totoche974/TLC-Mach3/src/manivelle.cpp

#include <Arduino.h>
#include <BleKeyboard.h>
#include <AiEsp32RotaryEncoder.h>

#include "manivelle.h"
#include "boutonMach3.h"
#include "screen.h"
#include "sleep.h"
#include "axe.h"

extern BleKeyboard keyboard;

#define ROTARY_ENCODER_STEPS 4

// extern BleKeyboard keyboard;

// instead of changing here, rather change numbers above
AiEsp32RotaryEncoder rotaryEncoder = AiEsp32RotaryEncoder(ROTARY_ENCODER_A_PIN, ROTARY_ENCODER_B_PIN,
                                                          ROTARY_ENCODER_BUTTON_PIN, ROTARY_ENCODER_VCC_PIN,
                                                          ROTARY_ENCODER_STEPS);

void initManivelle()
{
  // we must initialize rotary encoder
  rotaryEncoder.begin();

  rotaryEncoder.setup(
      []
      {
        rotaryEncoder.readEncoder_ISR();
      },
      [] {});

  rotaryEncoder.setAcceleration(250);
}

int previousEncoderPosition = 0;

const int KEY_2 = KEY_DOWN_ARROW;  // 40;
const int KEY_4 = KEY_LEFT_ARROW;  // 37; // KEY_LEFT_ARROW; //100; // 52; // X- : 100
const int KEY_6 = KEY_RIGHT_ARROW; // 39; // KEY_RIGHT_ARROW; // 102; // 54; // X+ : 102
const int KEY_8 = KEY_UP_ARROW;    // 38;

Axe currentAxe = Axe_x;
Axe previousAxe = Axe_x;
uint8_t selectedAxePositiveKey;
uint8_t selectedAxeNegativeKey;

void printAxe(Axe axeValue)
{
  switch (axeValue)
  {
  case Axe_x:
    printf("Axe X\n");
    screenSendMessage("   Axe X ");
    break;
  case Axe_y:
    printf("Axe Y\n");
    screenSendMessage("   Axe Y ");
    break;
  case Axe_z:
    printf("Axe Z\n");
    screenSendMessage("   Axe Z ");
    break;
  case Axe_a:
    printf("Axe A\n");
    screenSendMessage("   Axe A ");
    break;
  }
}

void selectAxe()
{
  currentAxe = getCurrentAxe();

  if (previousAxe != currentAxe)
  {
    switch (currentAxe)
    {
    case Axe_x:
    {
      selectedAxePositiveKey = KEY_4; // ACSII 4 : 52
      selectedAxeNegativeKey = KEY_6; // ACSII 6 : 54
      // Serial.print("currentAxe__X = ");
      // Serial.println(currentAxe);
      refreshSleepOriginTimestamp();
      break;
    }
    case Axe_y:
    {
      selectedAxePositiveKey = KEY_8; // ACSII 8 : 56
      selectedAxeNegativeKey = KEY_2; // ACSII 2 : 50
      // Serial.print("currentAxe__Y = ");
      // Serial.println(currentAxe);
      refreshSleepOriginTimestamp();
      break;
    }
    case Axe_z:
    {
      selectedAxePositiveKey = KEY_PAGE_UP;
      selectedAxeNegativeKey = KEY_PAGE_DOWN;
      // Serial.print("currentAxe__Z = ");
      // Serial.println(currentAxe);
      refreshSleepOriginTimestamp();
      break;
    }
    case Axe_a:
    {
      selectedAxePositiveKey = KEY_HOME;
      selectedAxeNegativeKey = KEY_END;
      // Serial.print("currentAxe__A = ");
      // Serial.println(currentAxe);
      refreshSleepOriginTimestamp();
      break;
    }
    }

    printAxe(currentAxe);
  }

  previousAxe = currentAxe;
}

void manivelle()
{
  // Serial.print("PIN_SECU_BT = "); Serial.println(digitalRead(PIN_SECU_BT));
  selectAxe();

  int currentEncoderPosition = -rotaryEncoder.readEncoder();
  int deltaEncoder = currentEncoderPosition - previousEncoderPosition;
  if ((digitalRead(PIN_SECU_BT) == LOW))
  { /* Touche Ctrl à droite ou à gauche*/
    refreshSleepOriginTimestamp();
    // Serial.print("PIN_SECU_BT = "); Serial.println(digitalRead(PIN_SECU_BT));
    if (deltaEncoder != 0)
    {
      printAxe(getCurrentAxe());
      printf("deltaEncoder: %d\n", deltaEncoder);
    }
    if (deltaEncoder > 0)
    {

      printf("CodRotIncrement > 0\n");
      // keyboard.press(KEY_LEFT_CTRL);
      printf("commande %d\n\n", selectedAxePositiveKey);
      keyboard.press(selectedAxePositiveKey);
      delay(50);
      keyboard.releaseAll();
    }
    else if (deltaEncoder < 0)
    {

      printf("CodRotIncrement < 0\n");
      // keyboard.press(KEY_LEFT_CTRL);
      printf("commande %d\n\n", selectedAxeNegativeKey);
      keyboard.press(selectedAxeNegativeKey);
      delay(50);
      keyboard.releaseAll();
    }
  }
  previousEncoderPosition = currentEncoderPosition;
}
