totoche974/TLC-Mach3/example_basic/fuel_jauge_lipo/fuel_jauge.cpp

//https://how2electronics.com/interfacing-max17043-lipo-fuel-gauge-ic-with-arduino/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

#include <SPI.h>
#include <Wire.h>
#include <LiFuelGauge.h>        //https://github.com/nlamprian/LiFuelGauge
#include <Adafruit_GFX.h>
#include <Adafruit_SSD1306.h>
 
#define SCREEN_WIDTH 128    // OLED display width, in pixels
#define SCREEN_HEIGHT 64    // OLED display height, in pixels
#define OLED_RESET     4    // Reset pin # (or -1 if sharing Arduino reset pin)
#define SCREEN_ADDRESS 0x3C // 0x3D for 128x64, 0x3C for 128x32
Adafruit_SSD1306 display(SCREEN_WIDTH, SCREEN_HEIGHT, &Wire, OLED_RESET);
 
 
void lowPower();
 
LiFuelGauge gauge(MAX17043, 0, lowPower);
 
volatile boolean alert = false;
 
 
void setup()
{
  Serial.begin(9600); // Initializes serial port
  if (!display.begin(SSD1306_SWITCHCAPVCC, SCREEN_ADDRESS))
  {
    Serial.println(F("SSD1306 allocation failed"));
    for (;;); // Don't proceed, loop forever
  }
  display.clearDisplay();
 
  // Waits for serial port to connect. Needed for Leonardo only
  while ( !Serial ) ;
 
  gauge.reset();  // Resets MAX17043
  delay(200);  // Waits for the initial measurements to be made
 
  // Sets the Alert Threshold to 10% of full capacity
  gauge.setAlertThreshold(10);
  Serial.println(String("Alert Threshold is set to ") +
                 gauge.getAlertThreshold() + '%');
}
 
 
void loop()
{
  Serial.print("SOC: ");
  Serial.print(gauge.getSOC());  // Gets the battery's state of charge
  Serial.print("%, VCELL: ");
  Serial.print(gauge.getVoltage());  // Gets the battery voltage
  Serial.println('V');
 
  display.setCursor(0, 10); //oled display
  display.setTextSize(2);
  display.setTextColor(WHITE);
  display.print("SOC:");
  display.print(gauge.getSOC());
  display.print("%");
 
  display.setCursor(0, 40); //oled display
  display.setTextSize(2);
  display.setTextColor(WHITE);
  display.print("VOL:");
  display.print(gauge.getVoltage());
  display.print("V");
 
  display.display();
  display.clearDisplay();
 
  if ( alert )
  {
    Serial.println("Beware, Low Power!");
    Serial.println("Finalizing operations...");
    gauge.clearAlertInterrupt();  // Resets the ALRT pin
    alert = false;
    Serial.println("Storing data...");
    Serial.println("Sending notification...");
    Serial.println("System operations are halted...");
    gauge.sleep();  // Forces the MAX17043 into sleep mode
    while ( true ) ;
  }
  delay(2000);
}
 
void lowPower()
{
  alert = true;
}
